alan-backlund/OldFashonedBikeComputer/Photos/P07.JPG

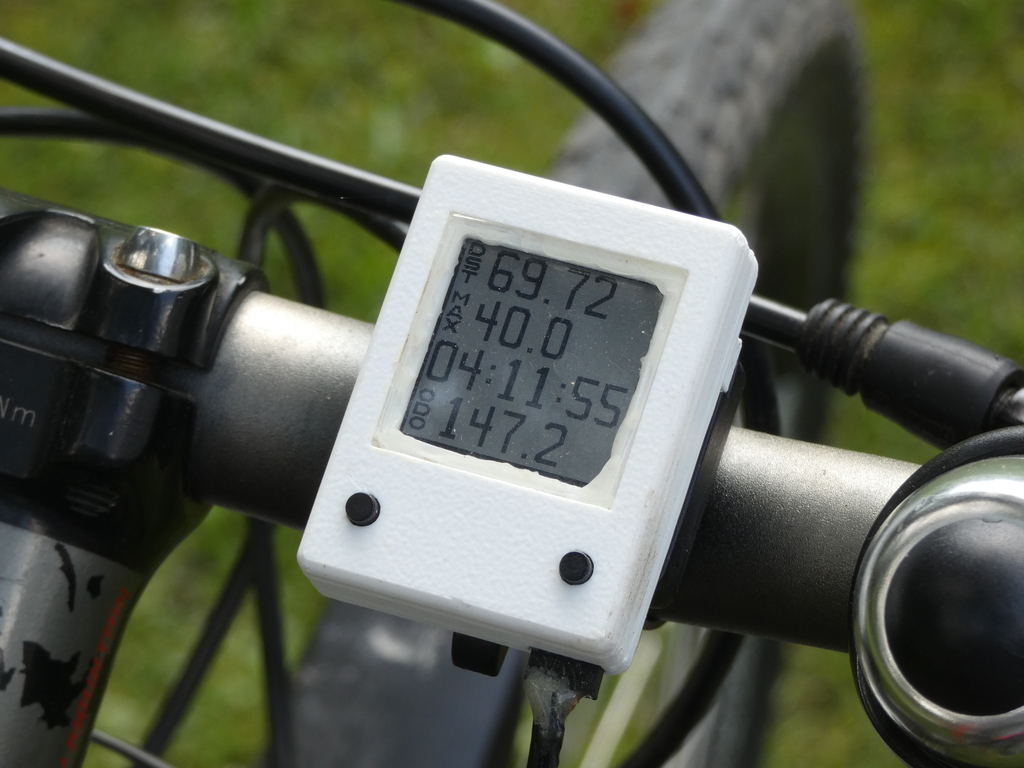
Photos/P07.JPG
