alan-backlund/OldFashonedBikeComputer/Photos/P13.JPG

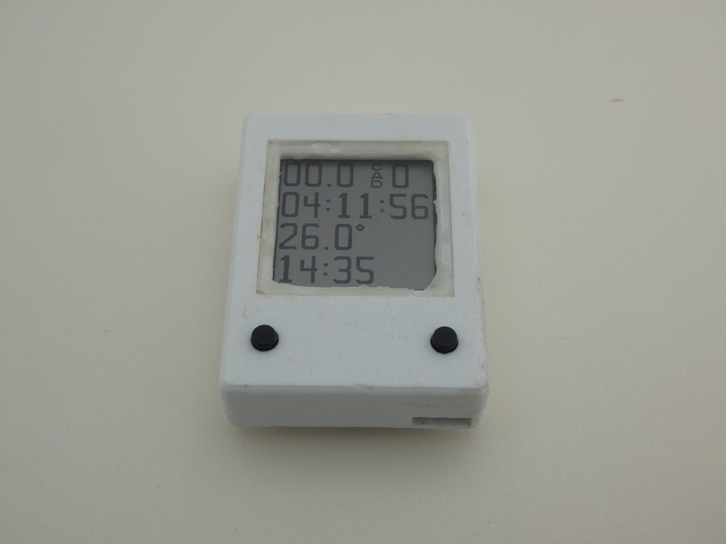
Photos/P13.JPG
