alan-backlund/OldFashonedBikeComputer/Photos/P16.JPG

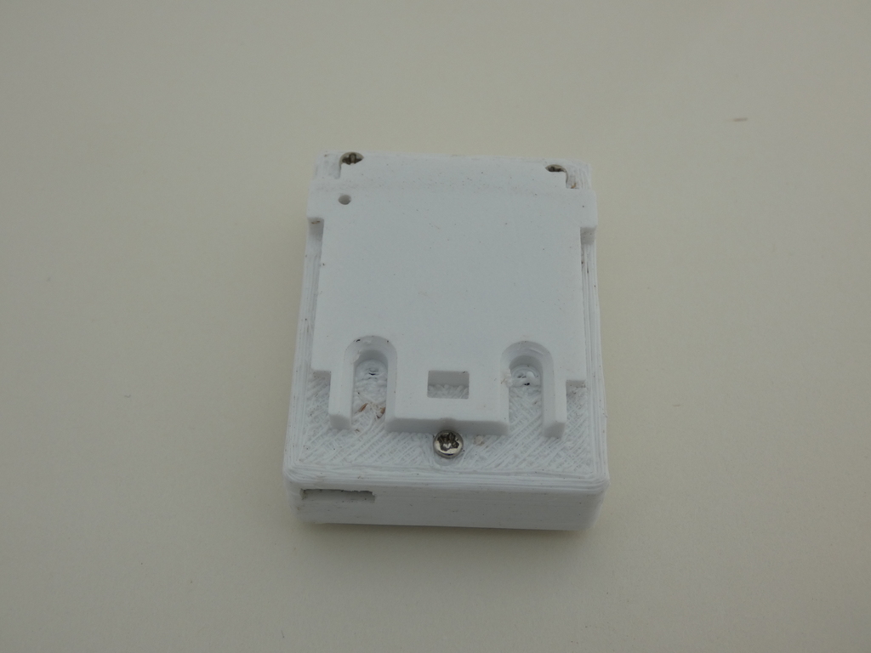
Photos/P16.JPG
