alan-backlund/OldFashonedBikeComputer/Photos/P18.JPG

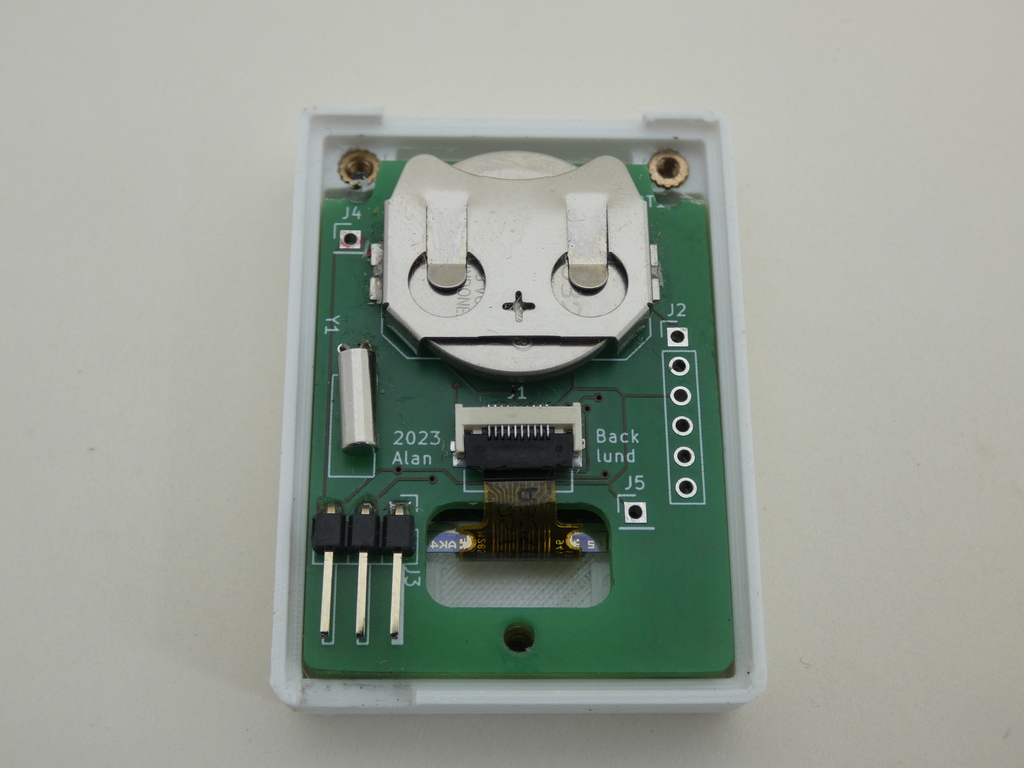
Photos/P18.JPG
