alan-backlund/OldFashonedBikeComputer/Photos/P21.JPG

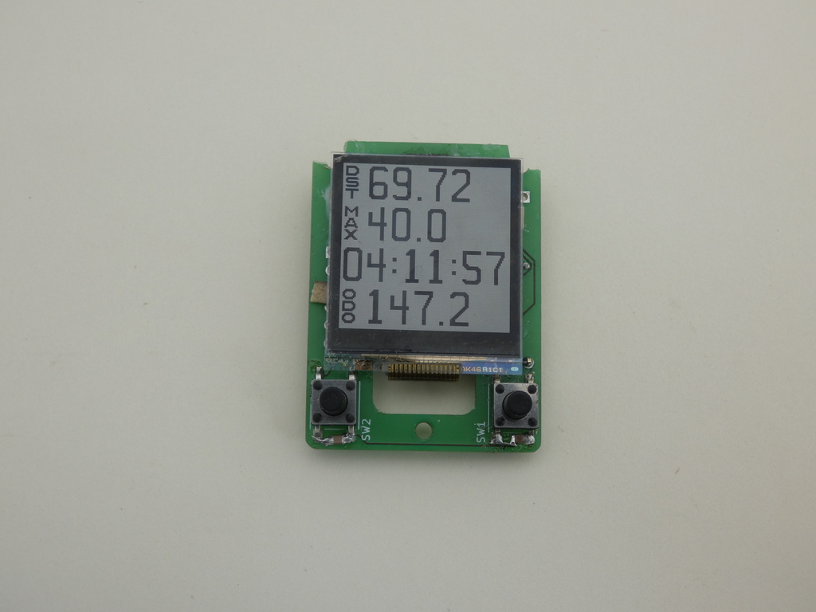
Photos/P21.JPG
