alan-backlund/OldFashonedBikeComputer/Photos/P23.JPG

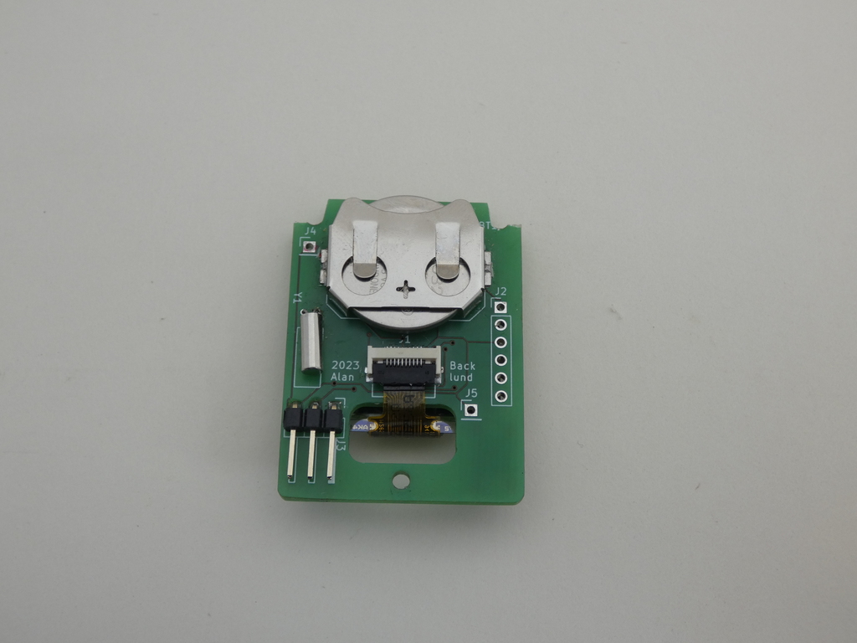
Photos/P23.JPG
