alan-backlund/OldFashonedBikeComputer/Code/Src/bitmaps.c

/*
 * bitmaps.c
 *
 *  Created on: Mar. 28, 2023
 *      Author: alan
 */

#include "bitmaps.h"

#if 0
// 'splash_128x128', 128x128px
const unsigned char epd_bitmap_splash_128x128 [] = {
	0x00, 0x00, 0x00, 0x00, 0x00, 0x00, 0x00, 0x00, 0x00, 0x00, 0x00, 0x00, 0x00, 0x00, 0x00, 0x00,
	0x00, 0x00, 0x00, 0x00, 0x00, 0x00, 0x00, 0x00, 0x00, 0x00, 0x00, 0x00, 0x00, 0x00, 0x00, 0x00,
	0x00, 0x00, 0x00, 0x00, 0x00, 0x00, 0x00, 0x00, 0x00, 0x00, 0x00, 0x00, 0x00, 0x00, 0x00, 0x00,
	0x00, 0x00, 0x00, 0x00, 0x00, 0x00, 0x00, 0x00, 0x00, 0x00, 0x00, 0x00, 0x00, 0x00, 0x00, 0x00,
	0x00, 0x00, 0x00, 0x00, 0x00, 0x00, 0x00, 0x00, 0x00, 0x00, 0x00, 0x00, 0x00, 0x00, 0x00, 0x00,
	0x00, 0x00, 0x00, 0x00, 0x00, 0x00, 0x00, 0x00, 0x00, 0x00, 0x00, 0x00, 0x00, 0x00, 0x00, 0x00,
	0x00, 0x00, 0x00, 0x00, 0x00, 0x00, 0x00, 0x00, 0x00, 0x00, 0x00, 0x00, 0x00, 0x00, 0x00, 0x00,
	0x00, 0x00, 0x00, 0x00, 0x00, 0x00, 0x00, 0x00, 0x00, 0x00, 0x00, 0x00, 0x00, 0x00, 0x00, 0x00,
	0x00, 0x00, 0x00, 0x00, 0x00, 0x00, 0x00, 0x00, 0x00, 0x00, 0x00, 0x00, 0x00, 0x00, 0x00, 0x00,
	0x00, 0x00, 0x00, 0x00, 0x00, 0x00, 0x00, 0x00, 0x00, 0x00, 0x00, 0x00, 0x00, 0x00, 0x00, 0x00,
	0x00, 0x00, 0x00, 0x00, 0x00, 0x00, 0x00, 0x00, 0x00, 0x00, 0x00, 0x00, 0x00, 0x00, 0x00, 0x00,
	0x00, 0x00, 0x00, 0x00, 0x00, 0x00, 0x00, 0x00, 0x00, 0x00, 0x00, 0x00, 0x00, 0x00, 0x00, 0x00,
	0x00, 0x00, 0x00, 0x00, 0x00, 0x00, 0x00, 0x00, 0x00, 0x00, 0x00, 0x00, 0x00, 0x00, 0x00, 0x00,
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
	0x03, 0xf0, 0x00, 0x03, 0xf0, 0x00, 0x03, 0xf0, 0x00, 0x03, 0xf0, 0x00, 0x03, 0xf0, 0x00, 0x03,
	0xf0, 0x00, 0x03, 0xf0, 0x00, 0x03, 0xf0, 0x00, 0x00, 0x00, 0x00, 0x00, 0x00, 0x00, 0x00, 0x00,
	0x00, 0x00, 0x00, 0x00, 0x00, 0x00, 0x00, 0x00, 0x00, 0x00, 0x00, 0x00, 0x00, 0x00, 0x00, 0x00
};

const bitmap_t bitmaps32[] = {
		{ epd_bitmap_0_18x32, 18, 32 },
		{ epd_bitmap_1_18x32, 18, 32 },
		{ epd_bitmap_2_18x32, 18, 32 },
		{ epd_bitmap_3_18x32, 18, 32 },
		{ epd_bitmap_4_18x32, 18, 32 },
		{ epd_bitmap_5_18x32, 18, 32 },
		{ epd_bitmap_6_18x32, 18, 32 },
		{ epd_bitmap_7_18x32, 18, 32 },
		{ epd_bitmap_8_18x32, 18, 32 },
		{ epd_bitmap_9_18x32, 18, 32 },
		{ epd_bitmap_A_18x32, 18, 32 },
		{ epd_bitmap_B_18x32, 18, 32 },
		{ epd_bitmap_C_18x32, 18, 32 },
		{ epd_bitmap_D_18x32, 18, 32 },
		{ epd_bitmap_E_18x32, 18, 32 },
		{ epd_bitmap_A_18x32, 18, 32 },
		{ epd_bitmap_A_18x32, 18, 32 },
		{ epd_bitmap_H_18x32, 18, 32 },
		{ epd_bitmap_I_18x32, 18, 32 },
		{ epd_bitmap_A_18x32, 18, 32 },
		{ epd_bitmap_K_18x32, 18, 32 },
		{ epd_bitmap_L_18x32, 18, 32 },
		{ epd_bitmap_M_18x32, 18, 32 },
		{ epd_bitmap_A_18x32, 18, 32 },
		{ epd_bitmap_O_18x32, 18, 32 },
		{ epd_bitmap_A_18x32, 18, 32 },
		{ epd_bitmap_A_18x32, 18, 32 },
		{ epd_bitmap_R_18x32, 18, 32 },
		{ epd_bitmap_A_18x32, 18, 32 },
		{ epd_bitmap_T_18x32, 18, 32 },
		{ epd_bitmap_A_18x32, 18, 32 },
		{ epd_bitmap_A_18x32, 18, 32 },
		{ epd_bitmap_W_18x32, 18, 32 },
		{ epd_bitmap_A_18x32, 18, 32 },
		{ epd_bitmap_A_18x32, 18, 32 },
		{ epd_bitmap_A_18x32, 18, 32 },
		{ epd_bitmap_cad_18x32, 18, 32 },
		{ epd_bitmap_colon_9x32, 9, 32 },
		{ epd_bitmap_degree_9x32, 9, 32 },
		{ epd_bitmap_dst_18x32, 18, 32 },
		{ epd_bitmap_max_18x32, 18, 32 },
		{ epd_bitmap_odo_18x32, 18, 32 },
		{ epd_bitmap_period_9x32, 9, 32 },
		{ epd_bitmap_r_arrow_18x32, 18, 32 },
		{ epd_bitmap_u_arrow_18x32, 18, 32 }
};

const uint8_t number_idx = 0;
const uint8_t alpha_idx = 10;
const uint8_t cad_idx = 36;
const uint8_t colon_idx = 37;
const uint8_t degree_idx = 38;
const uint8_t dst_idx = 39;
const uint8_t max_idx = 40;
const uint8_t odo_idx = 41;
const uint8_t period_idx = 42;
const uint8_t rarrow_idx = 43;
const uint8_t uarrow_idx = 44;


#if 0
// 32 bit tall bitmaps
// '0_20x32', 20x32px
const unsigned char epd_bitmap_0_20x32 [] = {
	0x00, 0x00, 0x00, 0x00, 0x00, 0x00, 0x03, 0xfc, 0x00, 0x07, 0xfe, 0x00, 0x0f, 0xff, 0x00, 0x17,
	0xfe, 0x80, 0x3b, 0xfd, 0xc0, 0x7c, 0x03, 0xe0, 0x7c, 0x03, 0xe0, 0x7c, 0x03, 0xe0, 0x7c, 0x03,
	0xe0, 0x7c, 0x03, 0xe0, 0x7c, 0x03, 0xe0, 0x7c, 0x03, 0xe0, 0x38, 0x01, 0xc0, 0x10, 0x00, 0x80,
	0x00, 0x00, 0x00, 0x10, 0x00, 0x80, 0x38, 0x01, 0xc0, 0x7c, 0x03, 0xe0, 0x7c, 0x03, 0xe0, 0x7c,
	0x03, 0xe0, 0x7c, 0x03, 0xe0, 0x7c, 0x03, 0xe0, 0x7c, 0x03, 0xe0, 0x7c, 0x03, 0xe0, 0x3b, 0xfd,
	0xc0, 0x17, 0xfe, 0x80, 0x0f, 0xff, 0x00, 0x07, 0xfe, 0x00, 0x03, 0xfc, 0x00, 0x00, 0x00, 0x00
};
// '1_20x32', 20x32px
const unsigned char epd_bitmap_1_20x32 [] = {
	0x00, 0x00, 0x00, 0x00, 0x00, 0x00, 0x00, 0x00, 0x00, 0x00, 0x00, 0x00, 0x00, 0x00, 0x00, 0x00,
	0x00, 0x80, 0x00, 0x01, 0xc0, 0x00, 0x03, 0xe0, 0x00, 0x03, 0xe0, 0x00, 0x03, 0xe0, 0x00, 0x03,
	0xe0, 0x00, 0x03, 0xe0, 0x00, 0x03, 0xe0, 0x00, 0x03, 0xe0, 0x00, 0x01, 0xc0, 0x00, 0x00, 0x80,
	0x00, 0x00, 0x00, 0x00, 0x00, 0x80, 0x00, 0x01, 0xc0, 0x00, 0x03, 0xe0, 0x00, 0x03, 0xe0, 0x00,
	0x03, 0xe0, 0x00, 0x03, 0xe0, 0x00, 0x03, 0xe0, 0x00, 0x03, 0xe0, 0x00, 0x03, 0xe0, 0x00, 0x01,
	0xc0, 0x00, 0x00, 0x80, 0x00, 0x00, 0x00, 0x00, 0x00, 0x00, 0x00, 0x00, 0x00, 0x00, 0x00, 0x00
};
// '2_20x32', 20x32px
const unsigned char epd_bitmap_2_20x32 [] = {
	0x00, 0x00, 0x00, 0x00, 0x00, 0x00, 0x03, 0xfc, 0x00, 0x07, 0xfe, 0x00, 0x0f, 0xff, 0x00, 0x07,
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
	0x60, 0x00, 0x00, 0x00
};

// Array of all bitmaps for convenience. (Total bytes used to store images in = 128)
const int epd_bitmap_allArray_LEN = 2;
const unsigned char* epd_bitmap_allArray[2] = {
	epd_bitmap_P_12x18,
	epd_bitmap_S_12x18
};
#endif
