alan-backlund/OldFashonedBikeComputer/Code/Inc/alt_main.h

/*
 * alt_main.h
 *
 *  Created on: May 5, 2023
 *      Author: alan
 */

#ifndef INC_ALT_MAIN_H_
#define INC_ALT_MAIN_H_

#ifdef __cplusplus
extern "C"
{
#endif

int alt_main();

#ifdef __cplusplus
}
#endif

#endif /* INC_ALT_MAIN_H_ */
